valeeBurgos/SumoBot/hardware/circuito/Placa/Placa.kicad_sch

## KiCad design hardware/circuito/Placa/Placa.kicad_sch (2023-06-13, last stored version)

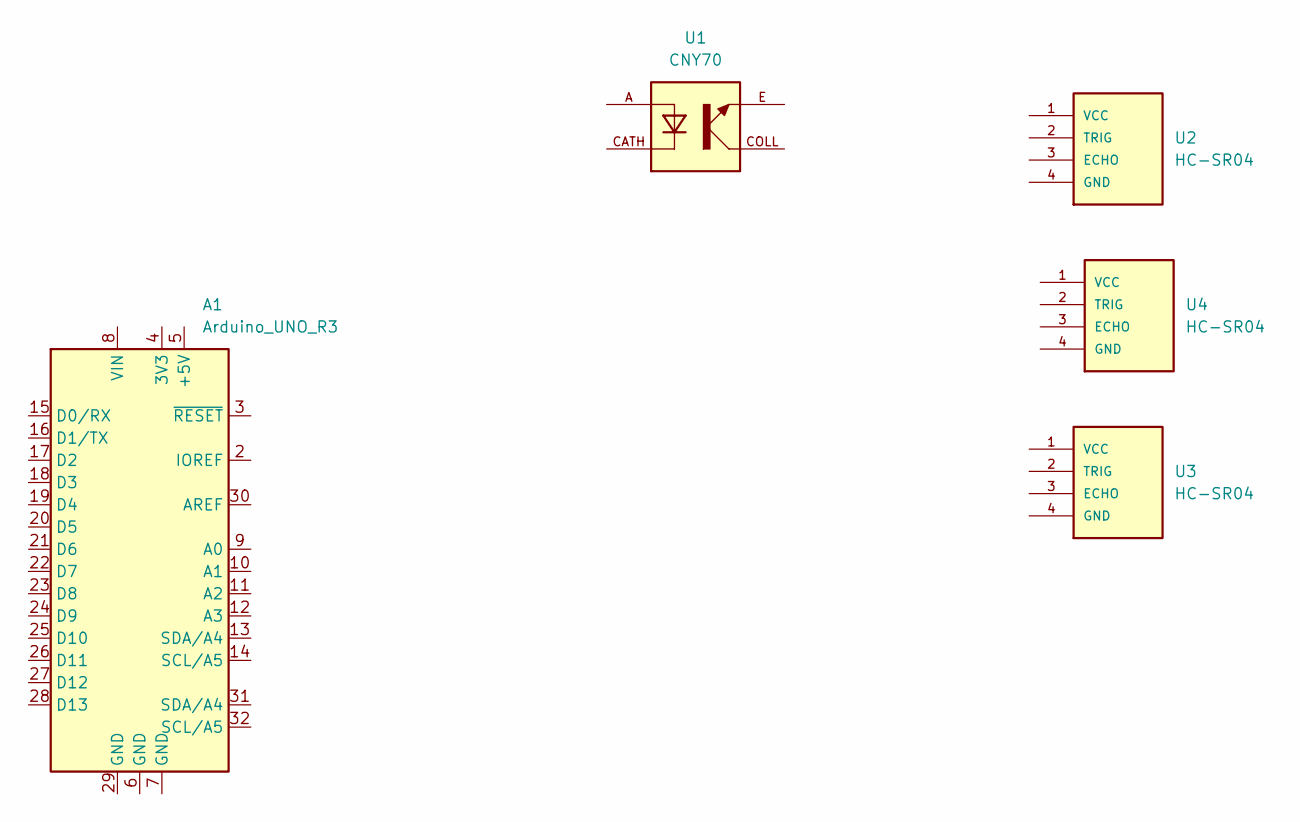
[picture p11: schematic Placa.kicad_sch]

Parts:
A1: Arduino_UNO_R3
U1: CNY70; PARTREV 1.8
U2, U3, U4: HC-SR04; XCVR_HC-SR04
